markoni985/NesCat/Resources/0fc3c4c95776b3c70a05941db097b029.jpg

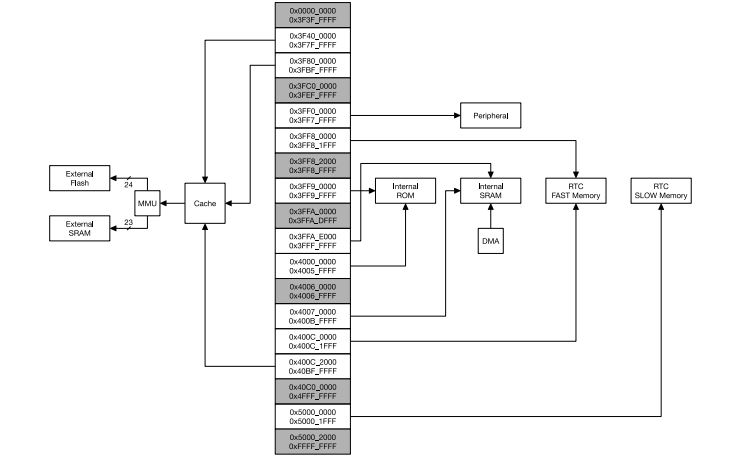
Resources/0fc3c4c95776b3c70a05941db097b029.jpg
