markoni985/NesCat/Resources/1-3inch-3-3V-ST7789-Driver-240x240-HD-IPS-Color-TFT-LCD-Display-Screen-Module.jpg

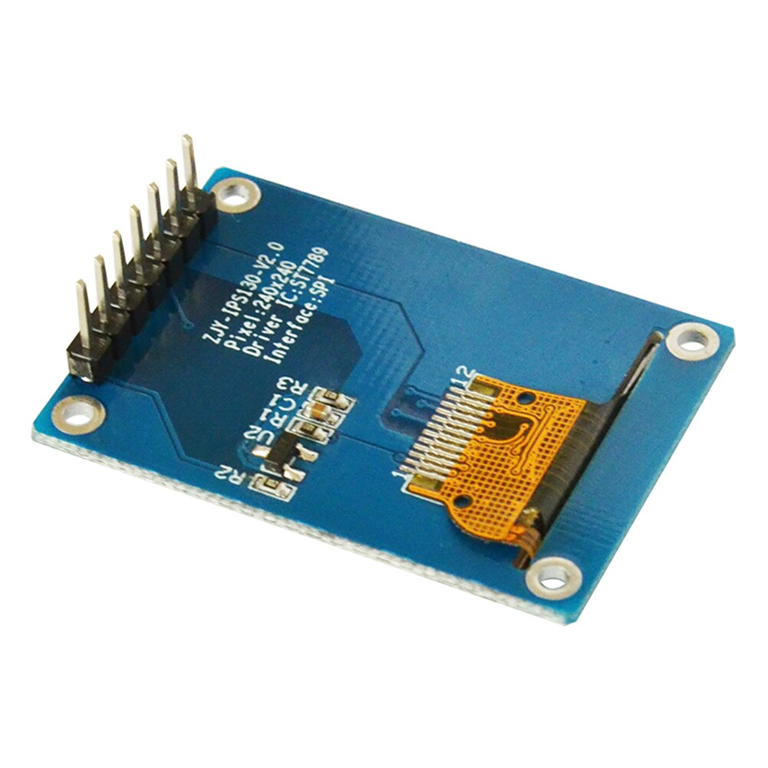
Resources/1-3inch-3-3V-ST7789-Driver-240x240-HD-IPS-Color-TFT-LCD-Display-Screen-Module.jpg
