markoni985/NesCat/Resources/05d26b62ef23cf1f85bcc10954f1f2cb.jpg

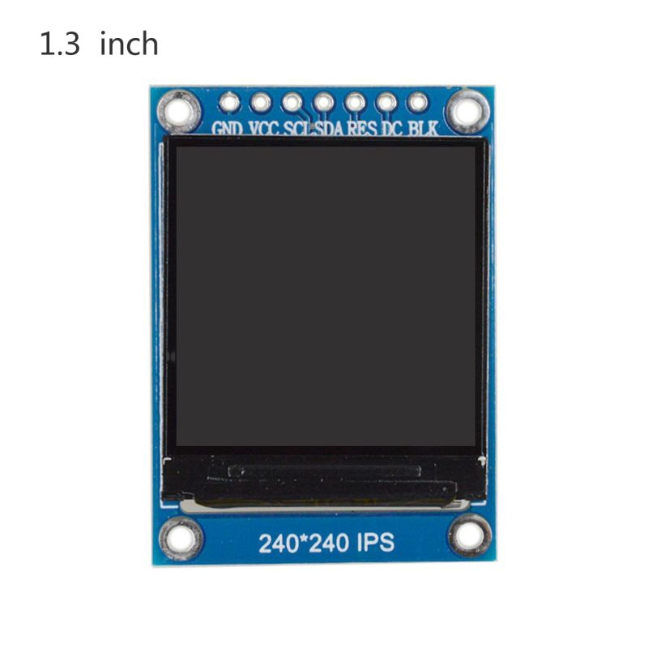
Resources/05d26b62ef23cf1f85bcc10954f1f2cb.jpg
