markoni985/NesCat/Resources/4605.970.jpg

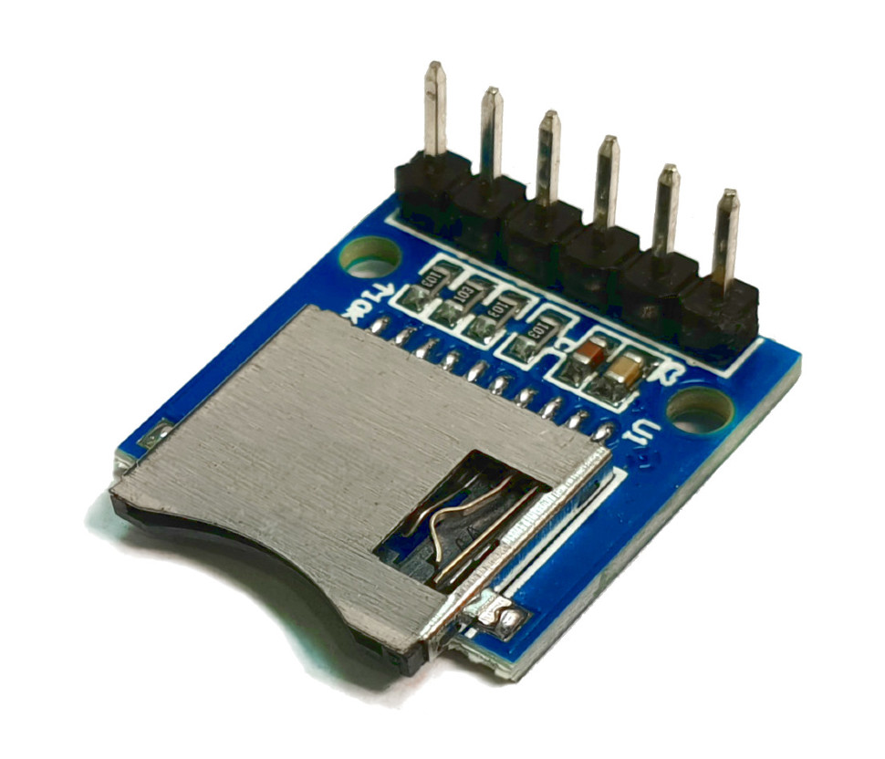
Resources/4605.970.jpg
