markoni985/NesCat/Resources/200608081906_tabulkaASCII.jpg

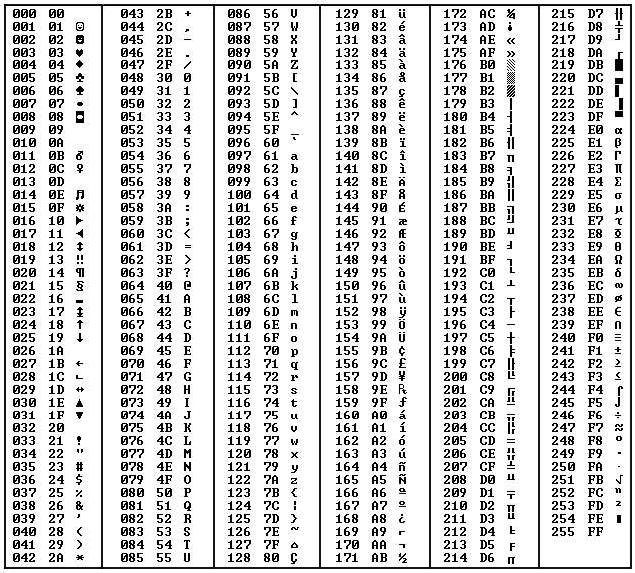
Resources/200608081906_tabulkaASCII.jpg
