markoni985/NesCat/Resources/Hf529fb3f73124e969ac0de5209e953b2o.png

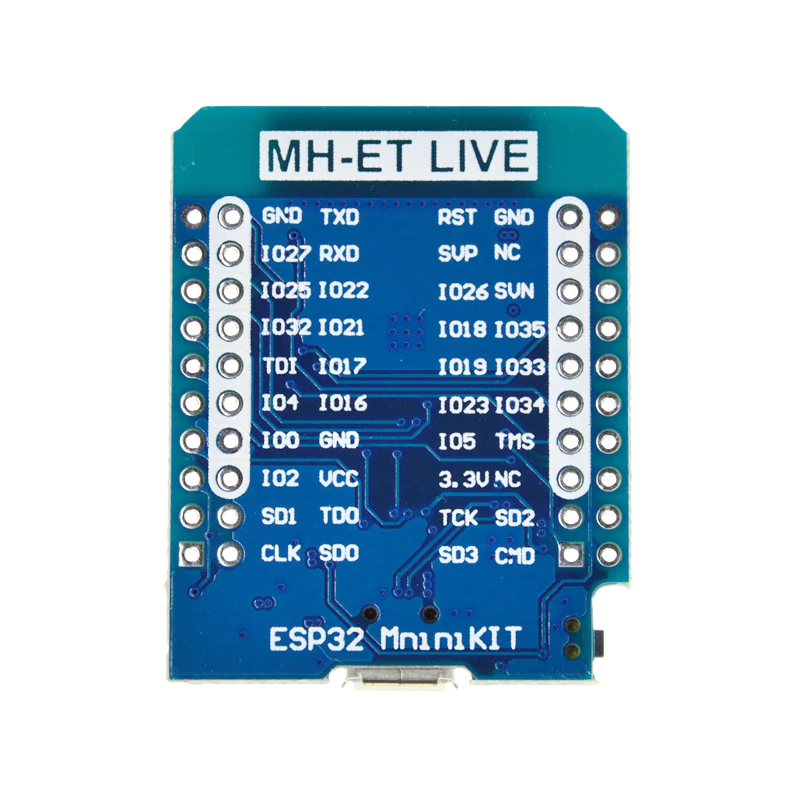
Resources/Hf529fb3f73124e969ac0de5209e953b2o.png
