markoni985/NesCat/Resources/HTB1bSiYRVXXXXb3XFXXq6xXFXXX2 (1).png

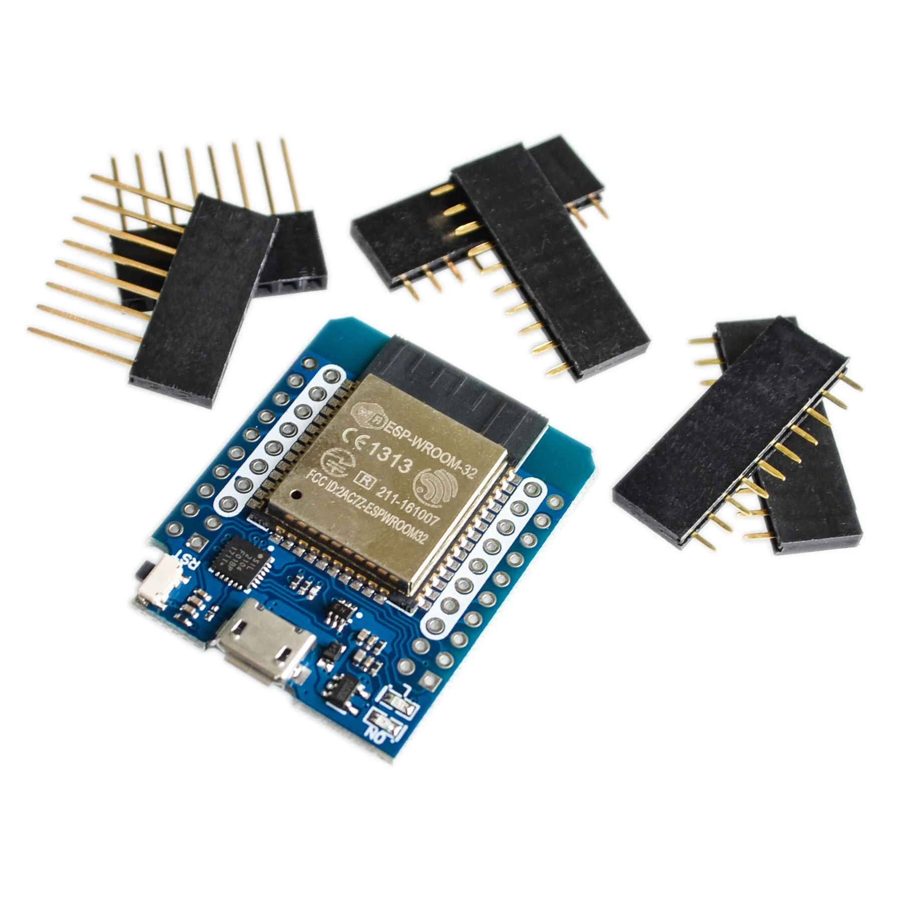
Resources/HTB1bSiYRVXXXXb3XFXXq6xXFXXX2 (1).png
