markoni985/NesCat/Resources/HTB1og9_RVXXXXbEXpXXq6xXFXXXt.png

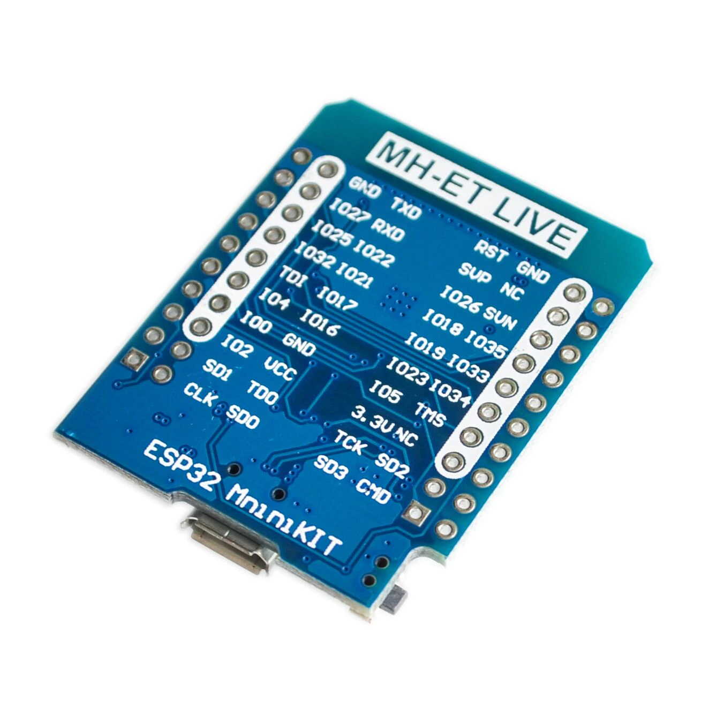
Resources/HTB1og9_RVXXXXbEXpXXq6xXFXXXt.png
