markoni985/NesCat/Resources/HTB10f1TRVXXXXagXVXXq6xXFXXXz.png

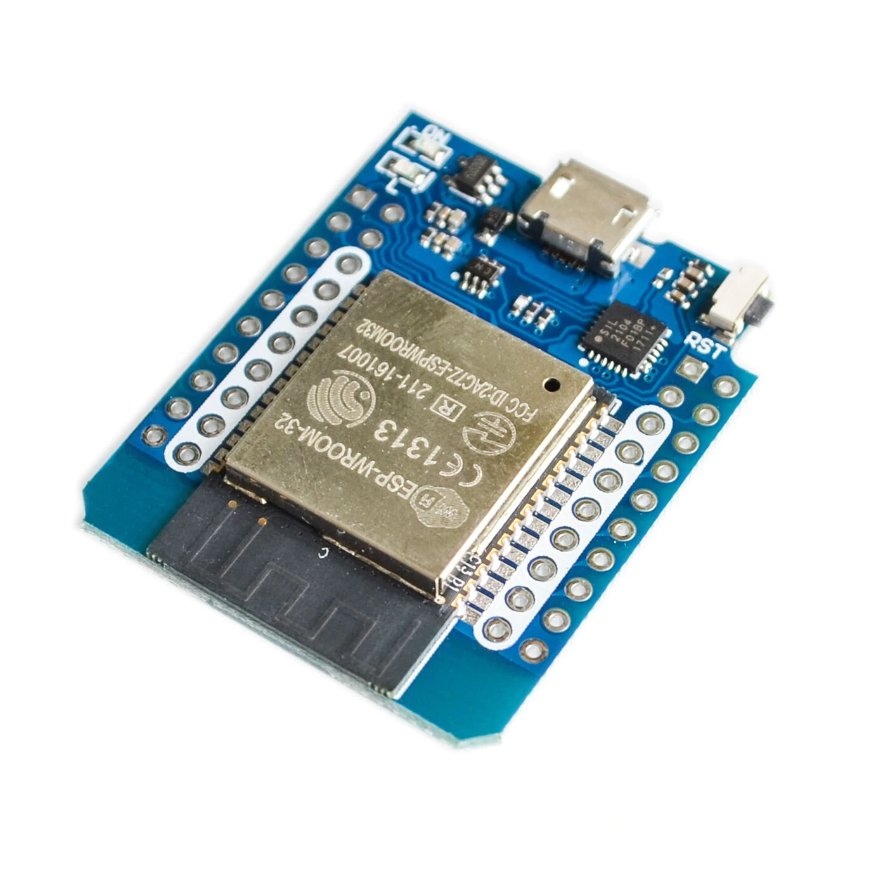
Resources/HTB10f1TRVXXXXagXVXXq6xXFXXXz.png
