markoni985/NesCat/Resources/Mini-SD-card-module-Micro-SD-card-module-Onboard-pop-up-MINI-SD-card-interface.png

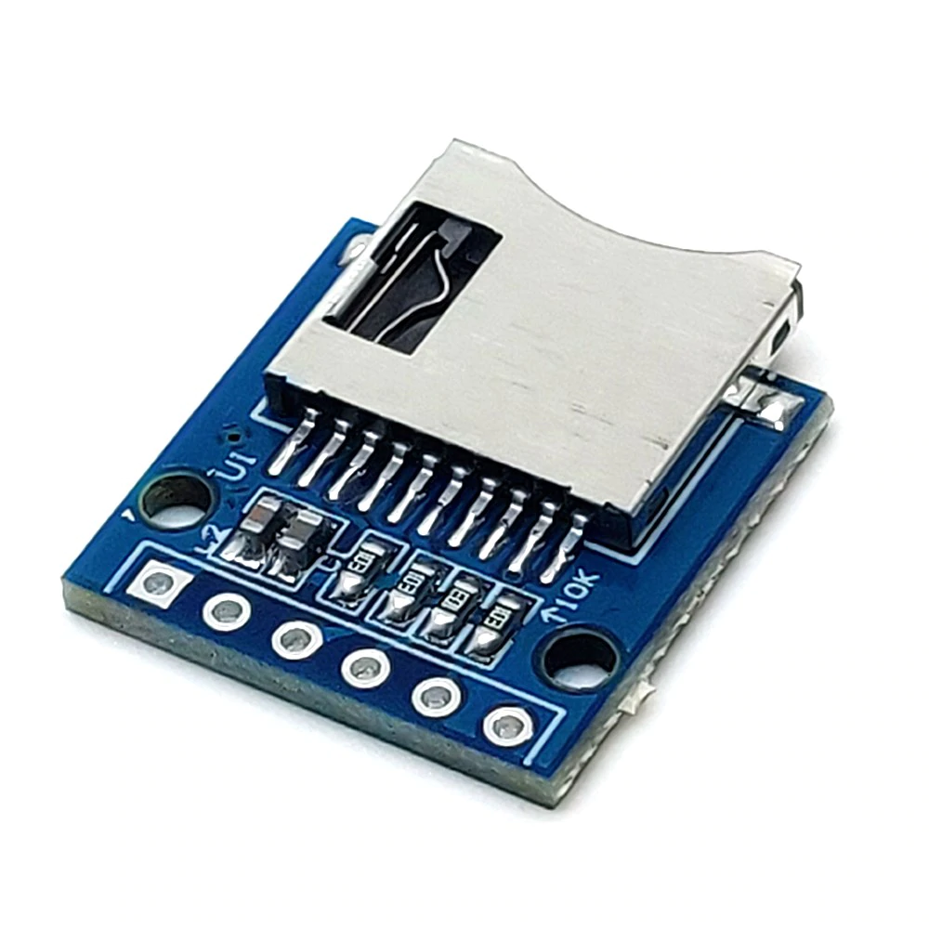
Resources/Mini-SD-card-module-Micro-SD-card-module-Onboard-pop-up-MINI-SD-card-interface.png
