markoni985/NesCat/Resources/NV_0718_Titus_Figure01.jpg

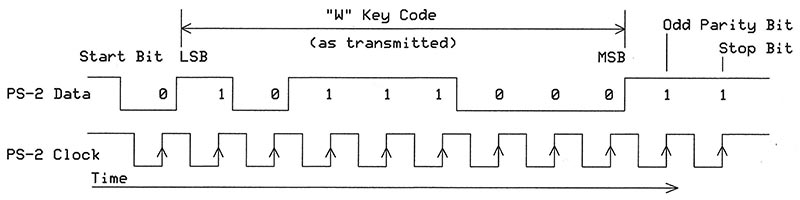
Resources/NV_0718_Titus_Figure01.jpg
