markoni985/NesCat/Retro8x16.c

// Retro8x16.c
// Font type    : Full (95 characters)
// Font size    : 8x16 pixels
// Memory usage : 1524 bytes


const char  Retro8x16[1524]={
0x08,0x10,0x20,0x5F,
0x00,0x00,0x00,0x00,0x00,0x00,0x00,0x00,0x00,0x00,0x00,0x00,0x00,0x00,0x00,0x00,  // <space>
0x10,0x10,0x10,0x10,0x10,0x10,0x10,0x10,0x10,0x10,0x00,0x00,0x10,0x10,0x00,0x00,  // !
0x24,0x24,0x24,0x24,0x24,0x24,0x00,0x00,0x00,0x00,0x00,0x00,0x00,0x00,0x00,0x00,  // "
0x24,0x24,0x24,0x24,0x7E,0x7E,0x24,0x24,0x7E,0x7E,0x24,0x24,0x24,0x24,0x00,0x00,  // #
0x10,0x10,0x3C,0x3C,0x50,0x50,0x38,0x38,0x14,0x14,0x78,0x78,0x10,0x10,0x00,0x00,  // $
0x00,0x00,0x62,0x62,0x64,0x64,0x08,0x08,0x10,0x10,0x26,0x26,0x46,0x46,0x00,0x00,  // %
0x30,0x30,0x48,0x48,0x48,0x48,0x30,0x30,0x4A,0x4A,0x44,0x44,0x3A,0x3A,0x00,0x00,  // &
0x10,0x10,0x10,0x10,0x10,0x10,0x00,0x00,0x00,0x00,0x00,0x00,0x00,0x00,0x00,0x00,  // '
0x10,0x10,0x20,0x20,0x40,0x40,0x40,0x40,0x40,0x40,0x20,0x20,0x10,0x10,0x00,0x00,  // (
0x10,0x10,0x08,0x08,0x04,0x04,0x04,0x04,0x04,0x04,0x08,0x08,0x10,0x10,0x00,0x00,  // )
0x10,0x10,0x54,0x54,0x38,0x38,0x10,0x10,0x38,0x38,0x54,0x54,0x10,0x10,0x00,0x00,  // *
0x00,0x00,0x10,0x10,0x10,0x10,0x7C,0x7C,0x10,0x10,0x10,0x10,0x00,0x00,0x00,0x00,  // +
0x00,0x00,0x00,0x00,0x00,0x00,0x00,0x00,0x08,0x08,0x08,0x08,0x10,0x10,0x00,0x00,  // ,
0x00,0x00,0x00,0x00,0x00,0x00,0x7E,0x7E,0x00,0x00,0x00,0x00,0x00,0x00,0x00,0x00,  // -
0x00,0x00,0x00,0x00,0x00,0x00,0x00,0x00,0x00,0x00,0x00,0x00,0x10,0x10,0x00,0x00,  // .
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
0x10,0x10,0x10,0x10,0x10,0x10,0x10,0x10,0x10,0x10,0x10,0x10,0x10,0x10,0x00,0x00,  // |
0x70,0x70,0x18,0x18,0x18,0x18,0x0E,0x0E,0x18,0x18,0x18,0x18,0x70,0x70,0x00,0x00,  // }
0x00,0x00,0x00,0x00,0x24,0x24,0x54,0x54,0x48,0x48,0x00,0x00,0x00,0x00,0x00,0x00,  // ~
};
